Stan-debakker/grap-6TWEA/school/foto robot/image4.png

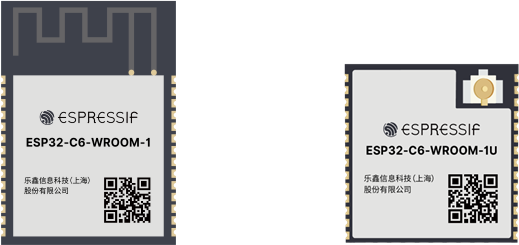
school/foto robot/image4.png
