Stan-debakker/grap-6TWEA/code_arduinoIDE/PI4IOE5V6416/PI4IOE5V6416.ino

#include "Wire.h"
#define ADDR 0x20
#define input__port_ADDR 0x00
#define output_port_ADDR 0x02
#define IO_dir_port_ADDR 0x04
#define PUL_EN_port_ADDR 0x46
#define PULDIR_port_ADDR 0x48
#define INT_EN_port_ADDR 0x4A
#define INT_SR_port_ADDR 0x4C

void setup() {
  Wire.begin(10,11);
  Serial.begin();
  set_output(0x55AA,output_port_ADDR);
}

void loop() {
  Serial.println(get_output(output_port_ADDR));
  delay(1000);
}

uint16_t get_output(uint8_t register_ADDR){
  uint16_t output=0;
  Wire.beginTransmission(ADDR);
  Wire.write(register_ADDR);
  Wire.endTransmission(false);
  Wire.requestFrom(ADDR,2,true);
  while(Wire.available()) {
    output=output<<8|Wire.read();
  }
  return output;
}
void set_output(uint16_t output, uint8_t register_ADDR){
  Wire.beginTransmission(ADDR);
  Wire.write(register_ADDR);
  Wire.write(output>>8);
  Wire.write(output&0xFF);
  Wire.endTransmission(true);
}
