Stan-debakker/grap-6TWEA/liberary/robot_ESP_addon/examples/machnetomerter_simpel_print/machnetomerter_simpel_print.ino

#include <robot_ESP_addon.h>

void setup() {
  robot_begin(0,false,false,false,true,false);  //start de robot

  Serial.println("machnetomer simple print");
  delay(100); //wacht tot de machnetometer is gestart
}

void loop() {
  bool is_mT=false;//mT(true) of µT(false)
  //vraag de data op en zet het in mT(true) of µT(false)
  converted_machnetometer data=convert_data_machnetometer(get_data_machnetometer(),is_mT);

  //vraag veldstrengte op en zet op de seriele monitor x,y,z
  Serial.print(data.magneet.x,4);
  Serial.print(',');
  Serial.print(data.magneet.y,4);
  Serial.print(',');
  Serial.print(data.magneet.z,4);
  Serial.print(',');
  //vraag de temperatuur op
  Serial.print(data.temp,4);
  Serial.print(',');
  //vraag de spanning op over de machnetometer
  Serial.println(data.volt,4);

  //wacht 10ms
  delay(10);
}
